zephray/NekoInk/utils/imgview/bluenoise.h

#ifdef DITHERING_BLUE_NOISE
#ifdef ENABLE_COLOR
int8_t noise_map[120][40] = {
    {14, 98, -98, 31, -24, 89, 6, 45, -75, 62, -32, 40, -68, 108, -82, -12, 122, -92, -41, 81, -116, -10, -73, 89, 21, -64, -88, 54, 126, -4, 65, -110, 121, -38, 41, -60, -79, -124, 36, -63, },
    {-109, 63, -47, 127, 70, -113, 103, -17, 116, -58, 95, -94, 1, -44, 65, -58, 36, 96, 21, -60, 5, 121, 53, -103, -26, 79, 102, -100, 25, 87, -46, 9, 30, -88, -114, 56, 87, 124, -32, 52, },
    {91, -59, -11, -86, 16, -68, 57, -100, 78, -124, 15, 74, 53, -111, 91, 14, -117, 57, -22, -105, 30, -35, -52, 38, 113, -45, 7, -17, -58, -126, -81, 105, -67, -25, 111, 0, -49, 25, -87, 4, },
    {-24, 39, 105, -126, -33, -6, 28, -48, -27, 34, -80, -15, 127, 25, -25, -97, 74, -3, -79, 110, 71, 94, -123, 14, -79, 62, -112, 47, 115, 74, 40, -9, 63, 91, 19, -104, -14, 74, -99, 114, },
    {-118, -76, 23, 52, 79, 98, -92, 123, 4, 106, -40, -105, -53, -76, 109, -38, -65, 124, -47, 44, -89, -68, -2, 75, -94, -10, 98, -71, -30, 13, -41, -98, 47, -54, -123, 80, 37, -66, -40, 68, },
    {-4, 85, -43, 113, -105, -57, 43, -75, -110, 63, 45, 99, -4, 82, 36, 49, 10, 85, -120, 17, -15, 59, 104, -27, 123, 31, -54, 22, -89, 94, -114, 119, -75, 7, -33, 122, -79, 99, 48, 14, },
    {125, -96, -66, 6, -16, 66, 13, 89, -9, -63, 18, -93, 70, -127, -19, -88, -107, -9, 102, -32, -101, 27, -58, -113, -40, 55, 84, -120, 65, 0, 33, -23, 103, 71, -91, 55, -5, -22, -113, -52, },
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
    {-81, 111, -31, -94, 76, 28, -86, 3, 71, 33, -89, 22, 65, 8, -123, 127, 27, 11, -37, -113, 17, 79, -78, -8, 64, -100, -58, 119, 100, -106, 65, 93, },
};
#endif
#endif
